noahp/kl2_qfn_breakout/sw/docs/debug_common.png

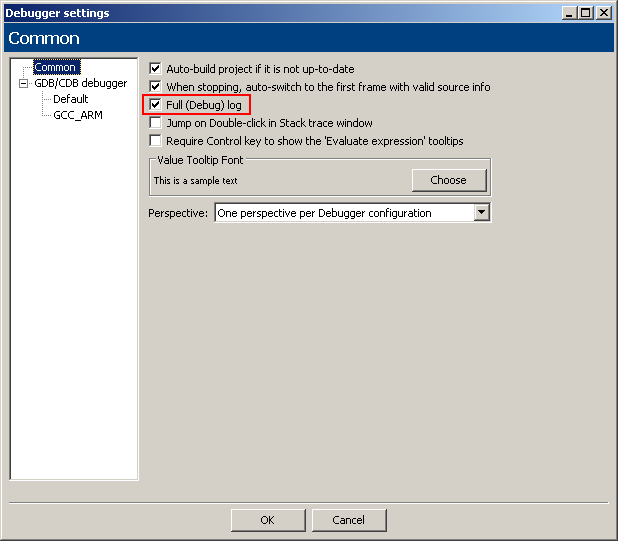
sw/docs/debug_common.png
