noahp/kl2_qfn_breakout/sw/docs/gdb_debug_cfg.png

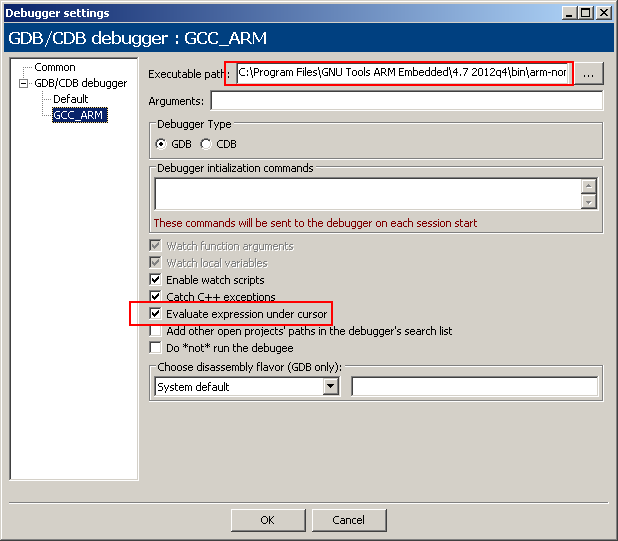
sw/docs/gdb_debug_cfg.png
